enblack0/Hidden-HID-v2/photos/IMG_20250104_114501_754.jpg

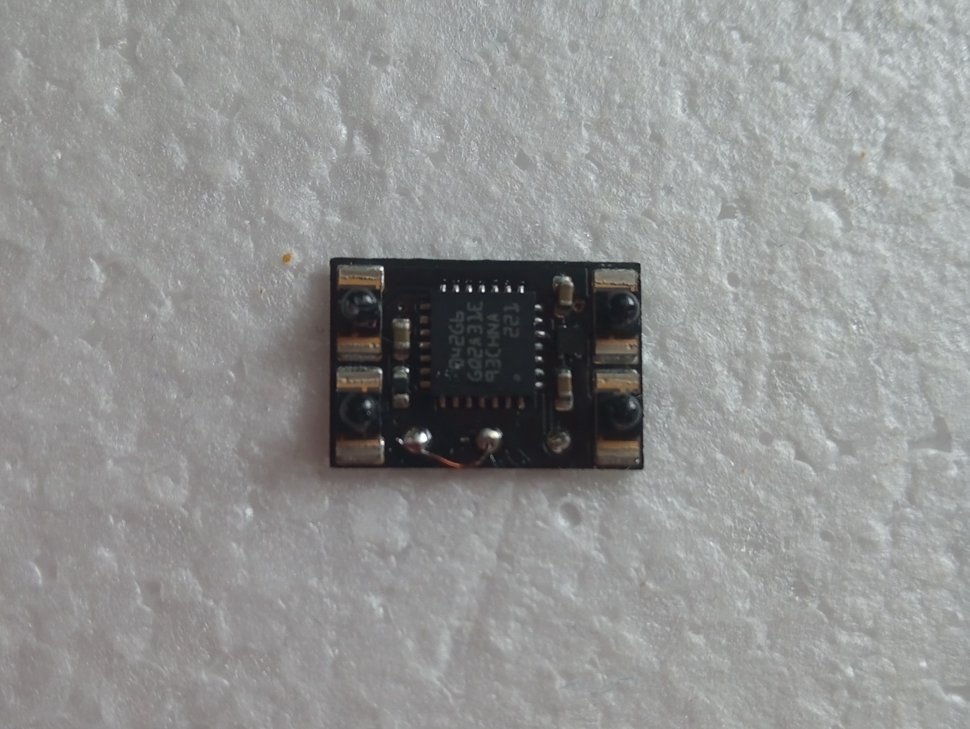
photos/IMG_20250104_114501_754.jpg
