enblack0/Hidden-HID-v2/photos/IMG_20250118_132318_155.jpg

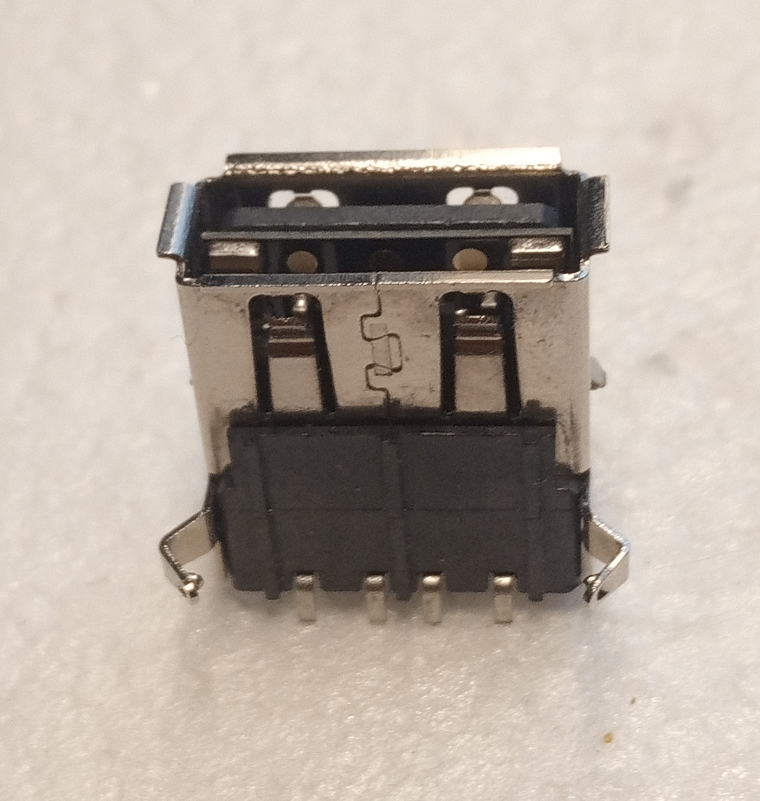
photos/IMG_20250118_132318_155.jpg
