enblack0/Hidden-HID-v2/photos/IMG_20250118_132709_884.jpg

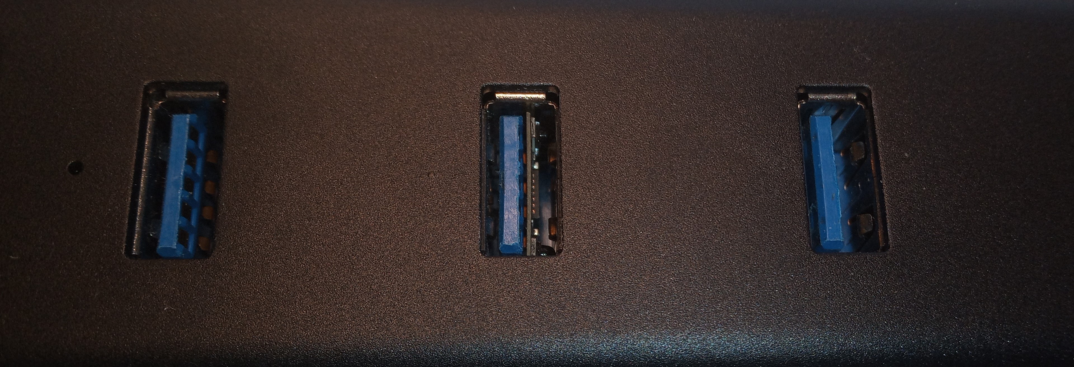
photos/IMG_20250118_132709_884.jpg
