enblack0/Hidden-HID-v2/photos/IMG_20250118_132744_294.jpg

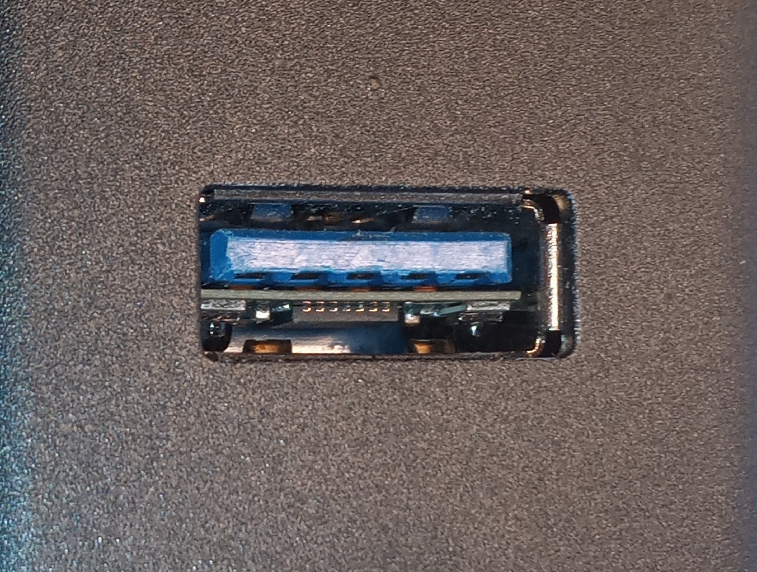
photos/IMG_20250118_132744_294.jpg
